Ryzee119/spi2par2019/images/prog2.jpg

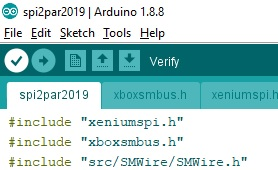
images/prog2.jpg
